Kariiboo/colomn-drill-repair/Pictures/IMG_20171223_090146.jpg

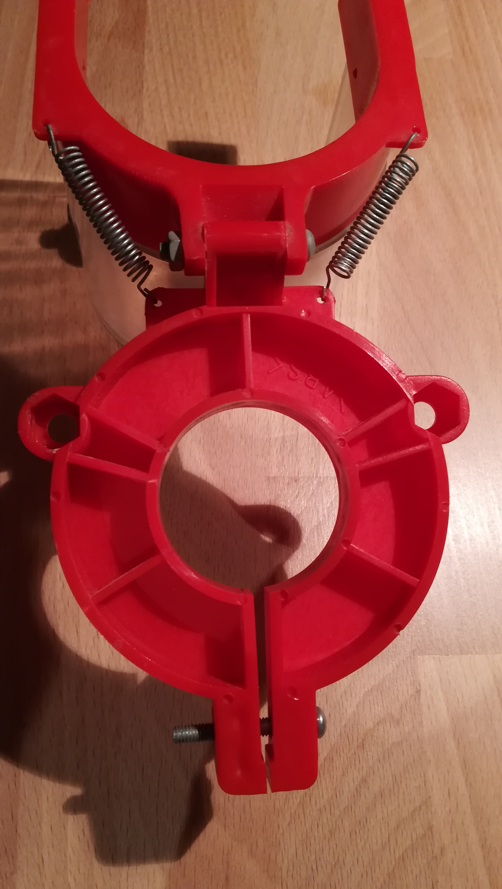
Pictures/IMG_20171223_090146.jpg
