Kariiboo/colomn-drill-repair/Pictures/IMG_20171223_090157.jpg

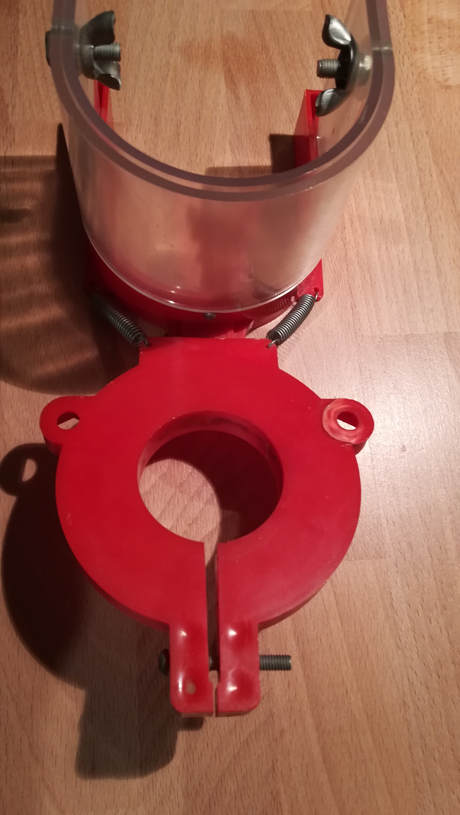
Pictures/IMG_20171223_090157.jpg
