Kariiboo/colomn-drill-repair/Pictures/IMG_20171223_090221.jpg

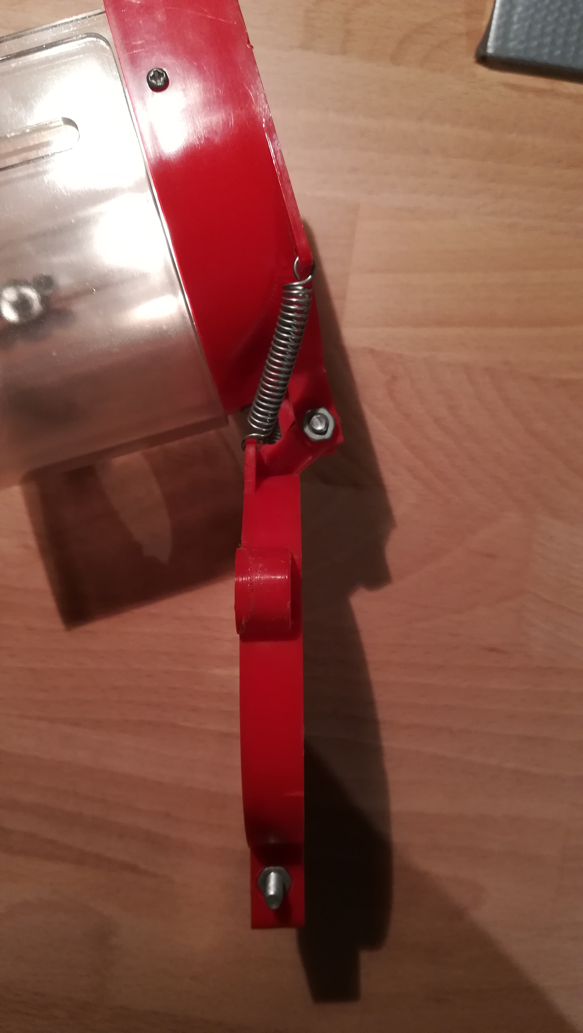
Pictures/IMG_20171223_090221.jpg
