Kariiboo/colomn-drill-repair/Pictures/IMG_20171223_090229.jpg

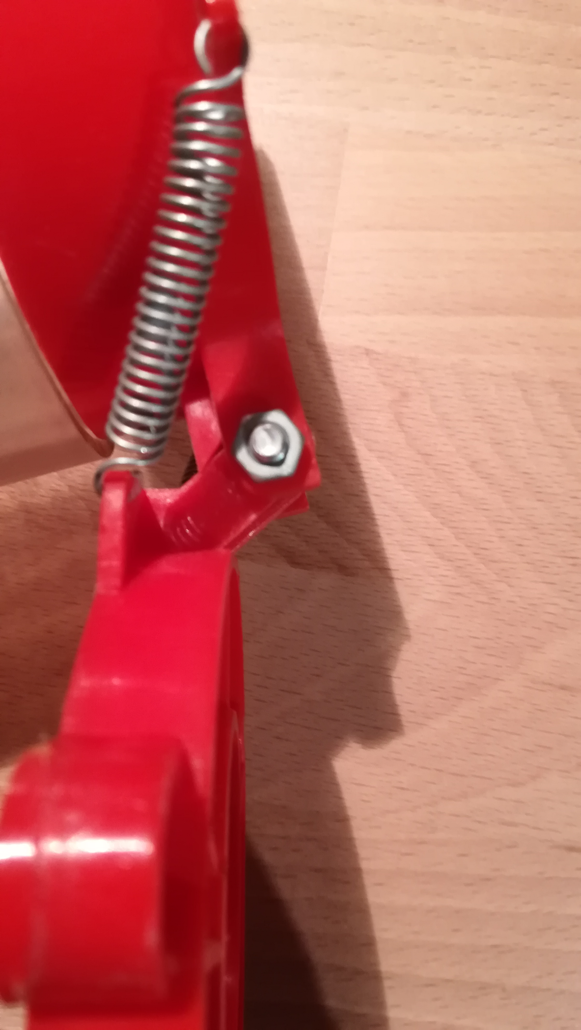
Pictures/IMG_20171223_090229.jpg
