Kariiboo/colomn-drill-repair/Pictures/IMG_20171230_145909.jpg

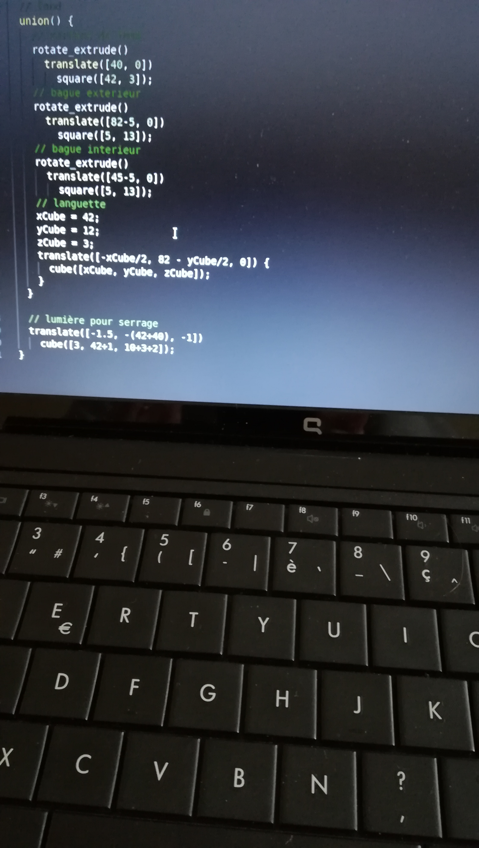
Pictures/IMG_20171230_145909.jpg
