Kariiboo/colomn-drill-repair/Pictures/IMG_20180110_222524.jpg

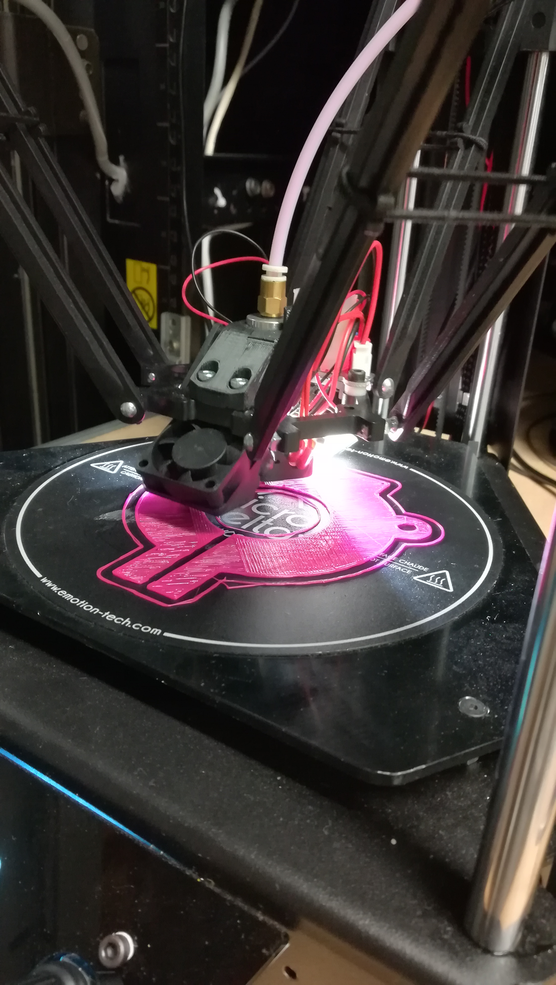
Pictures/IMG_20180110_222524.jpg
