Kariiboo/colomn-drill-repair/Pictures/IMG_20180110_222527_1.jpg

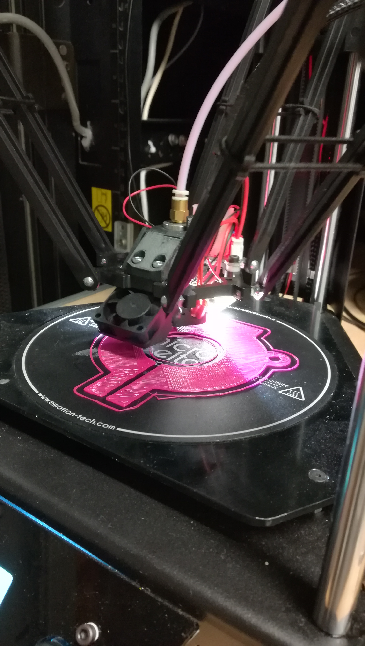
Pictures/IMG_20180110_222527_1.jpg
