Kariiboo/colomn-drill-repair/Pictures/IMG_20180110_222535.jpg

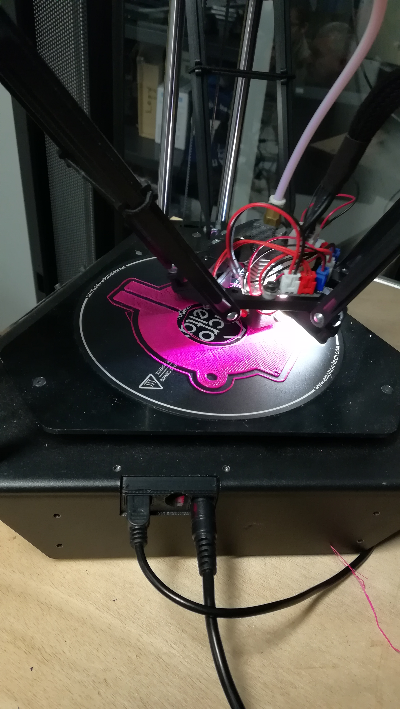
Pictures/IMG_20180110_222535.jpg
