Kariiboo/colomn-drill-repair/Pictures/IMG_20180415_153439.jpg

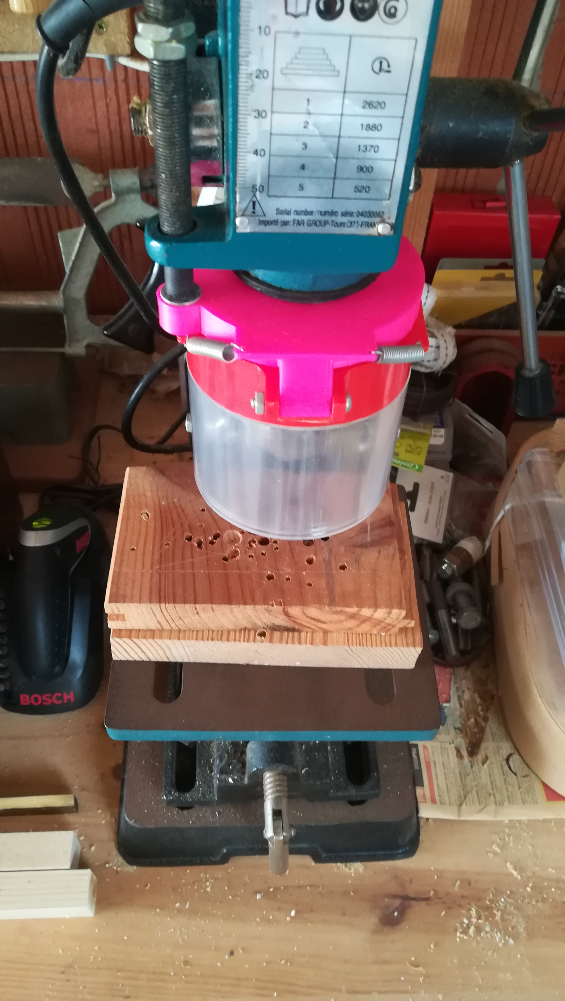
Pictures/IMG_20180415_153439.jpg
